DrMikeG/Lightsaber2021/readme_imgs/adafruit_products_TB6612_RasPi_stepper_bb.jpg

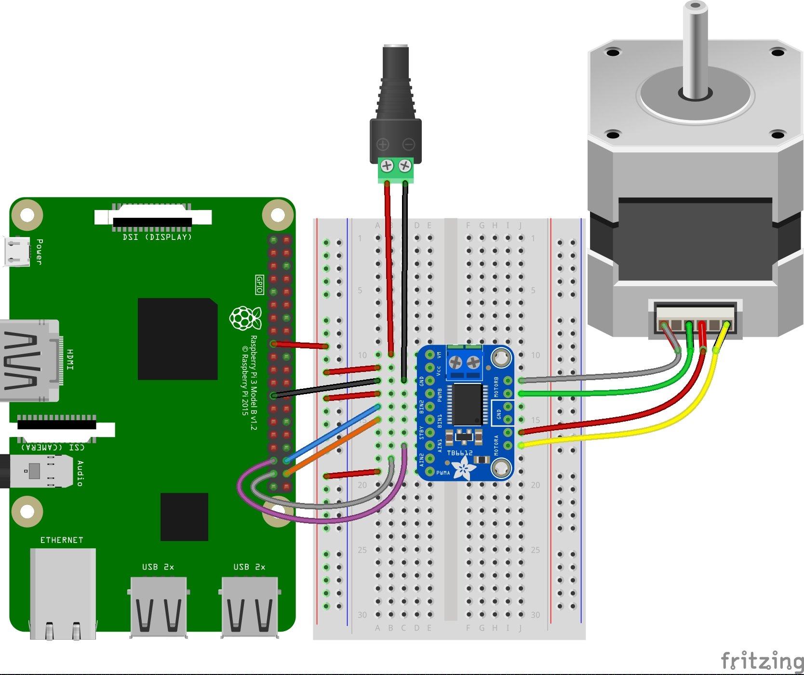
readme_imgs/adafruit_products_TB6612_RasPi_stepper_bb.jpg
