DrMikeG/Lightsaber2021/readme_imgs/circuitpython_FeatherM0ExpressPot_bb.jpg

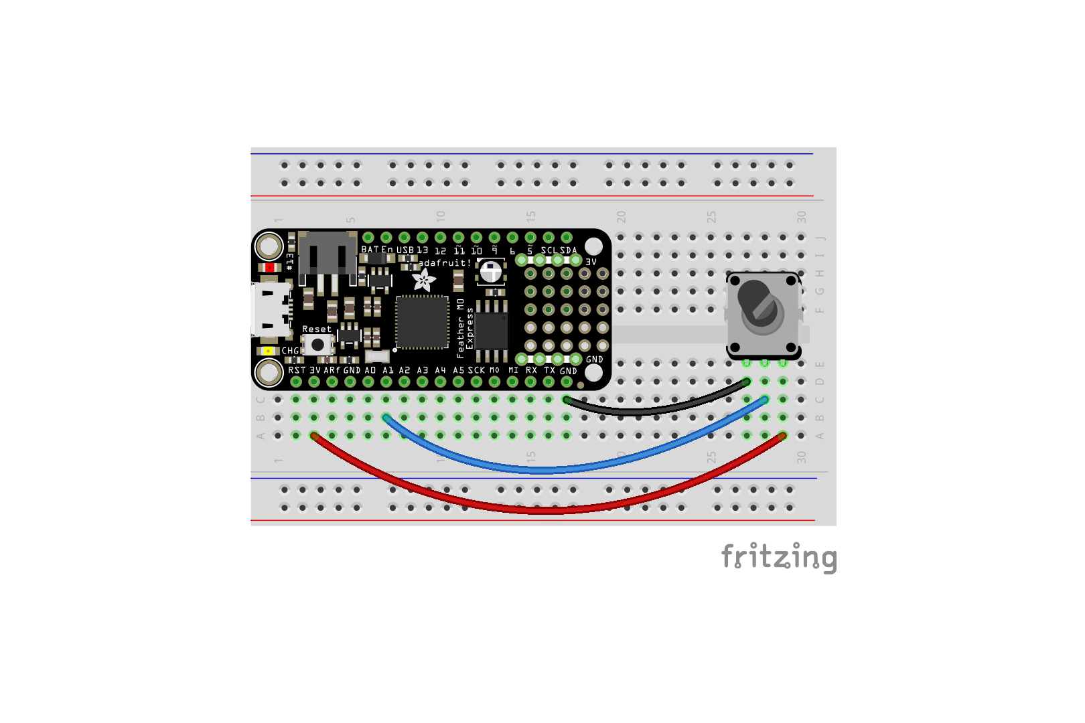
readme_imgs/circuitpython_FeatherM0ExpressPot_bb.jpg
