DrMikeG/Lightsaber2021/readme_imgs/Push-Pull-Pots.jpg

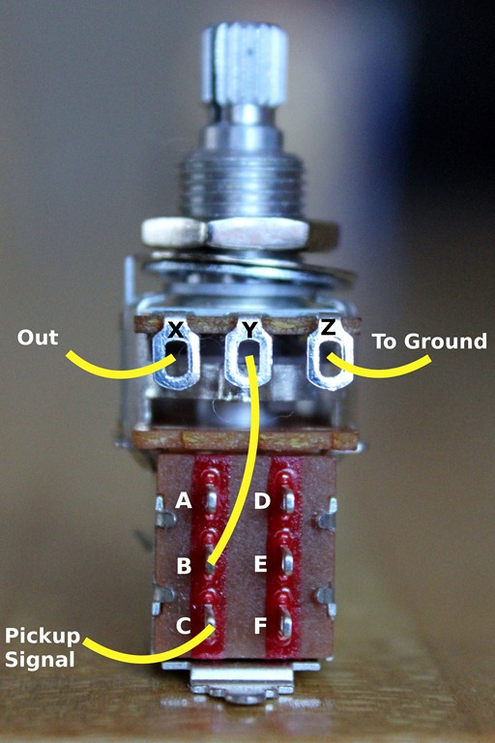
readme_imgs/Push-Pull-Pots.jpg
