DrMikeG/Lightsaber2021/readme_imgs/robotics___cnc_pico_motor_party_rev1_1.jpg

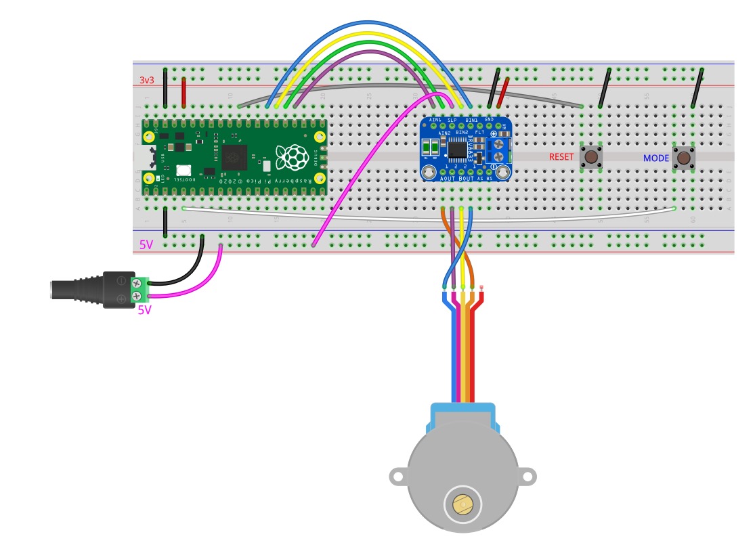
readme_imgs/robotics___cnc_pico_motor_party_rev1_1.jpg
