DrMikeG/Lightsaber2021/PropMaker_LightSaber_parts/images/1a010fce53cceae1ac56e08a0f01a03c_preview_featured.jpg

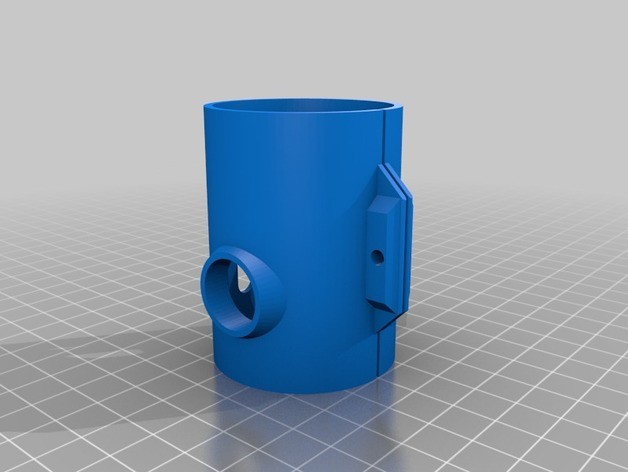
PropMaker_LightSaber_parts/images/1a010fce53cceae1ac56e08a0f01a03c_preview_featured.jpg
