DrMikeG/Lightsaber2021/PropMaker_LightSaber_parts/images/1e69a8725f925d21972f3fd7c3aa4356_preview_featured.jpg

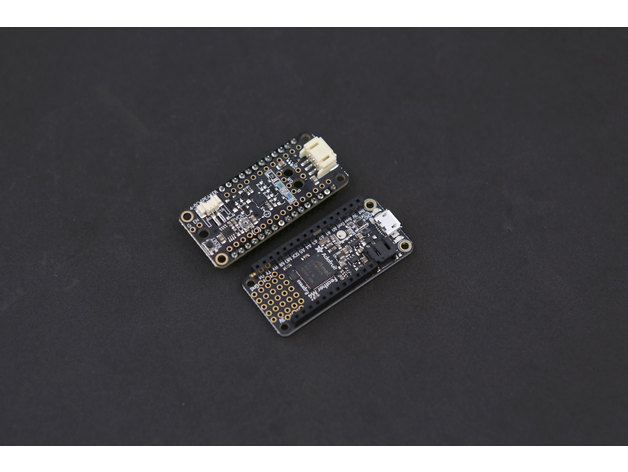
PropMaker_LightSaber_parts/images/1e69a8725f925d21972f3fd7c3aa4356_preview_featured.jpg
