DrMikeG/Lightsaber2021/PropMaker_LightSaber_parts/images/2a8135917e567a2e131dea8dfad645b4_preview_featured.jpg

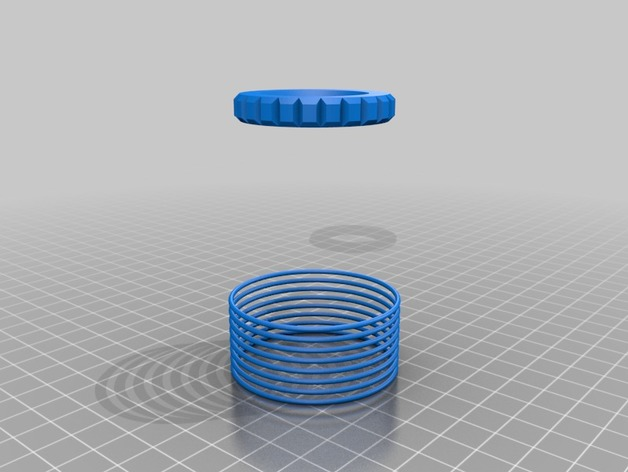
PropMaker_LightSaber_parts/images/2a8135917e567a2e131dea8dfad645b4_preview_featured.jpg
