DrMikeG/Lightsaber2021/PropMaker_LightSaber_parts/images/2da9e44c6a2c6dd28a2d1fa6bc67a7b8_preview_featured.jpg

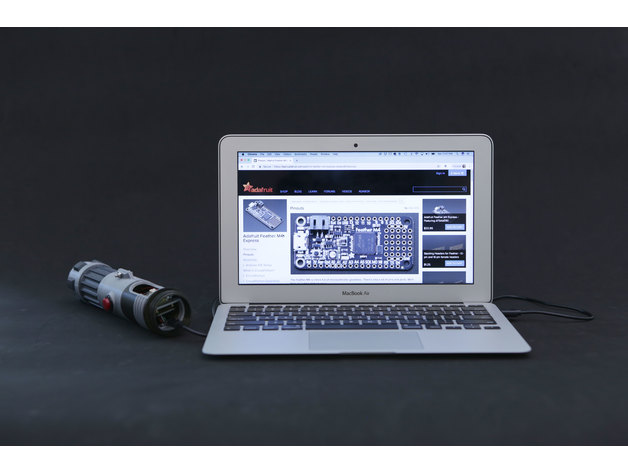
PropMaker_LightSaber_parts/images/2da9e44c6a2c6dd28a2d1fa6bc67a7b8_preview_featured.jpg
