DrMikeG/Lightsaber2021/PropMaker_LightSaber_parts/images/4b34a5e26058de7491f0624bd9dabff6_preview_featured.jpg

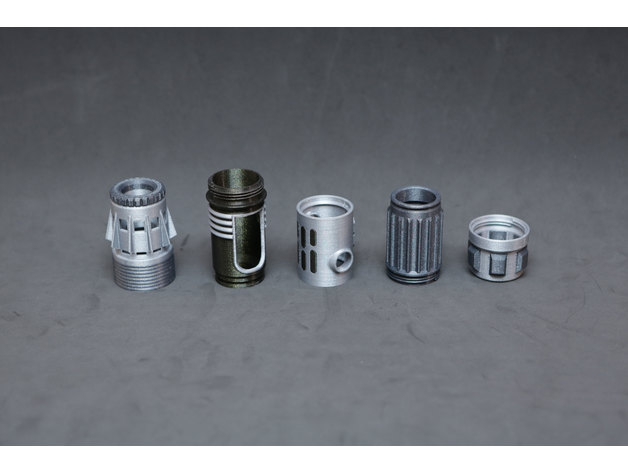
PropMaker_LightSaber_parts/images/4b34a5e26058de7491f0624bd9dabff6_preview_featured.jpg
