DrMikeG/Lightsaber2021/PropMaker_LightSaber_parts/images/5d4f0135c1b05c36856adea3e5bb96b0_preview_featured.jpg

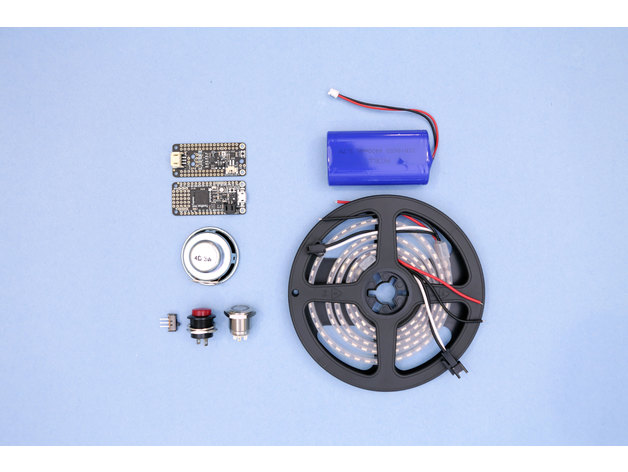
PropMaker_LightSaber_parts/images/5d4f0135c1b05c36856adea3e5bb96b0_preview_featured.jpg
