DrMikeG/Lightsaber2021/PropMaker_LightSaber_parts/images/5df59d24ba937bf4968393d7608ab2a4_preview_featured.jpg

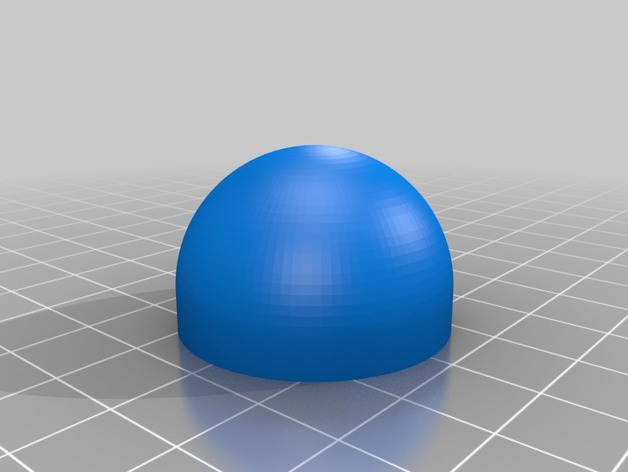
PropMaker_LightSaber_parts/images/5df59d24ba937bf4968393d7608ab2a4_preview_featured.jpg
