DrMikeG/Lightsaber2021/PropMaker_LightSaber_parts/images/6a94d57f789392ea3bade564f7ede461_preview_featured.jpg

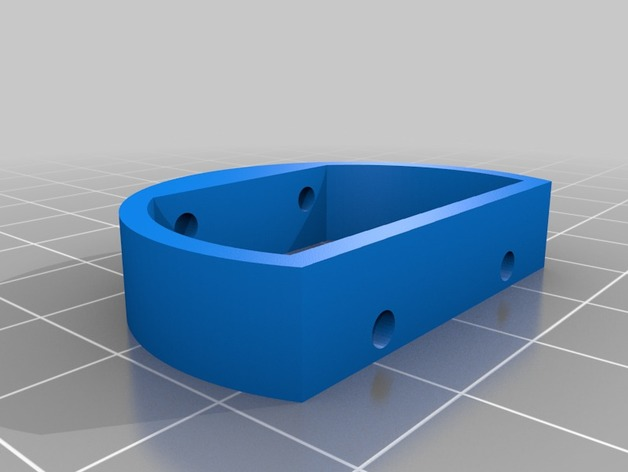
PropMaker_LightSaber_parts/images/6a94d57f789392ea3bade564f7ede461_preview_featured.jpg
