DrMikeG/Lightsaber2021/PropMaker_LightSaber_parts/images/6db03532910a7f3d1109cc5c1272abf1_preview_featured.jpg

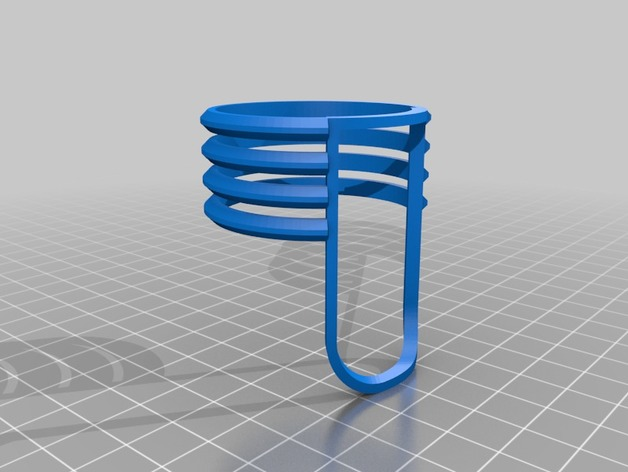
PropMaker_LightSaber_parts/images/6db03532910a7f3d1109cc5c1272abf1_preview_featured.jpg
