DrMikeG/Lightsaber2021/PropMaker_LightSaber_parts/images/37e0bd1d6943ed3912d0251d179854dd_preview_featured.jpg

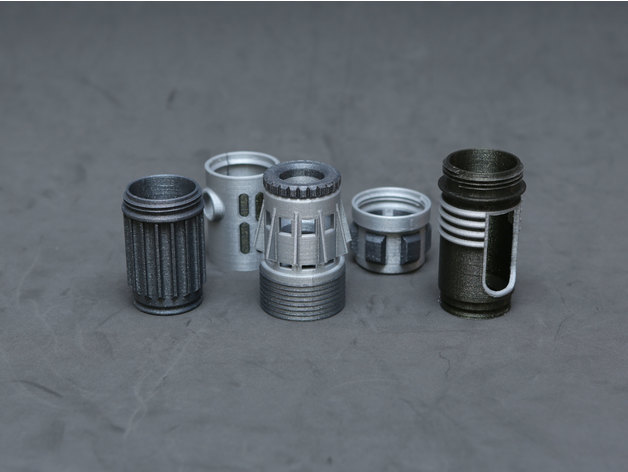
PropMaker_LightSaber_parts/images/37e0bd1d6943ed3912d0251d179854dd_preview_featured.jpg
