DrMikeG/Lightsaber2021/PropMaker_LightSaber_parts/images/97de8b0ce98b56c74fa4f8f1e708dd70_preview_featured.jpg

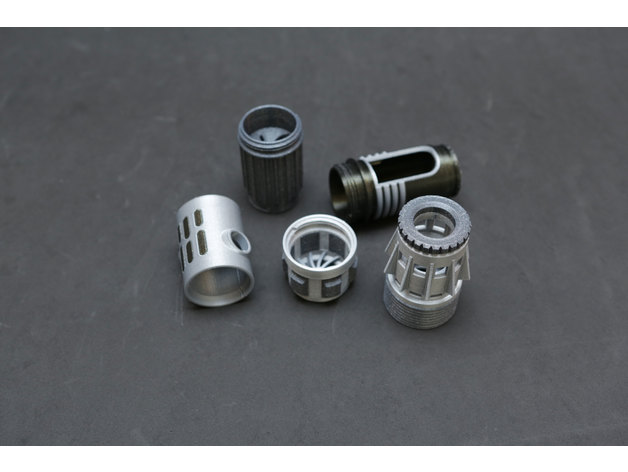
PropMaker_LightSaber_parts/images/97de8b0ce98b56c74fa4f8f1e708dd70_preview_featured.jpg
