DrMikeG/Lightsaber2021/PropMaker_LightSaber_parts/images/725ce138789fb76293f7604e14eeec18_preview_featured.jpg

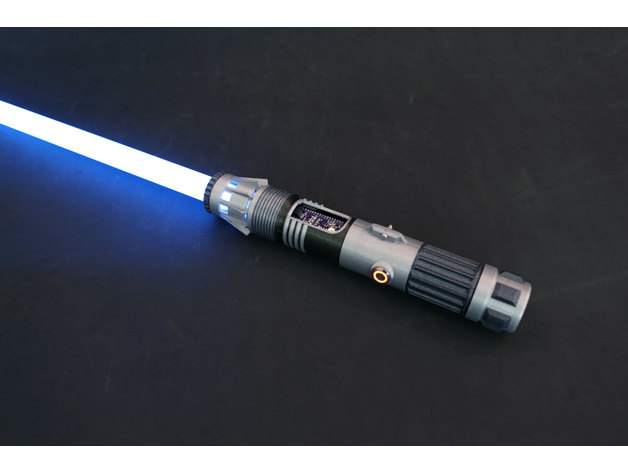
PropMaker_LightSaber_parts/images/725ce138789fb76293f7604e14eeec18_preview_featured.jpg
