DrMikeG/Lightsaber2021/PropMaker_LightSaber_parts/images/0832f2631e51cb04565bbbbad0c780f9_preview_featured.jpg

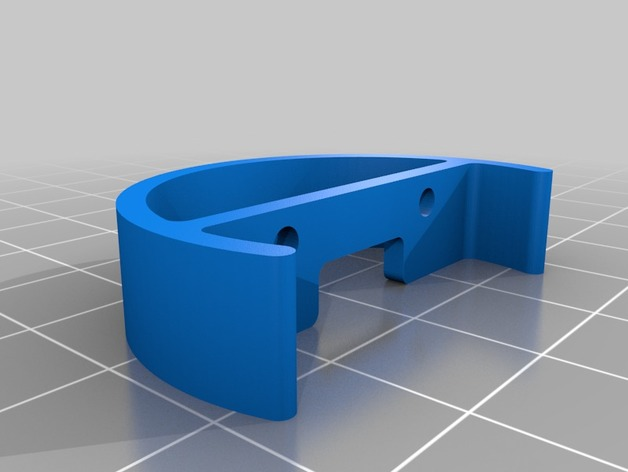
PropMaker_LightSaber_parts/images/0832f2631e51cb04565bbbbad0c780f9_preview_featured.jpg
