DrMikeG/Lightsaber2021/PropMaker_LightSaber_parts/images/8650a7c8c6fc7279c6bf91dc1d254c43_preview_featured.jpg

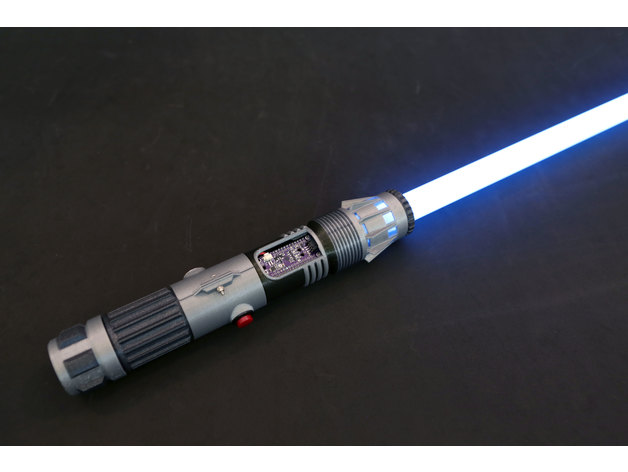
PropMaker_LightSaber_parts/images/8650a7c8c6fc7279c6bf91dc1d254c43_preview_featured.jpg
