DrMikeG/Lightsaber2021/PropMaker_LightSaber_parts/images/abff16dfec9813ce94c728e3b09540b0_preview_featured.jpg

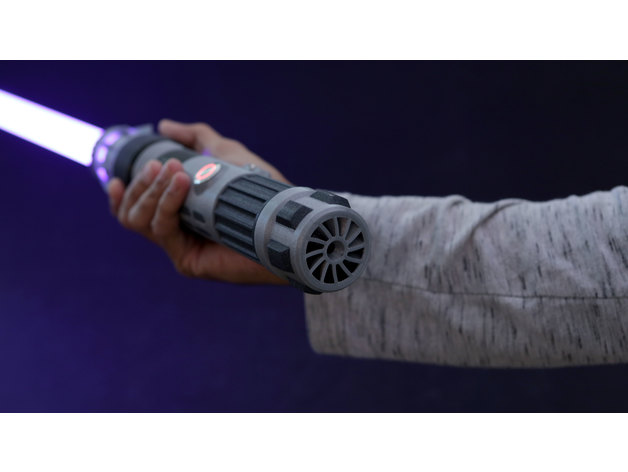
PropMaker_LightSaber_parts/images/abff16dfec9813ce94c728e3b09540b0_preview_featured.jpg
