DrMikeG/Lightsaber2021/PropMaker_LightSaber_parts/images/ad7b09b95d9fd7f6477543790e99b3de_preview_featured.jpg

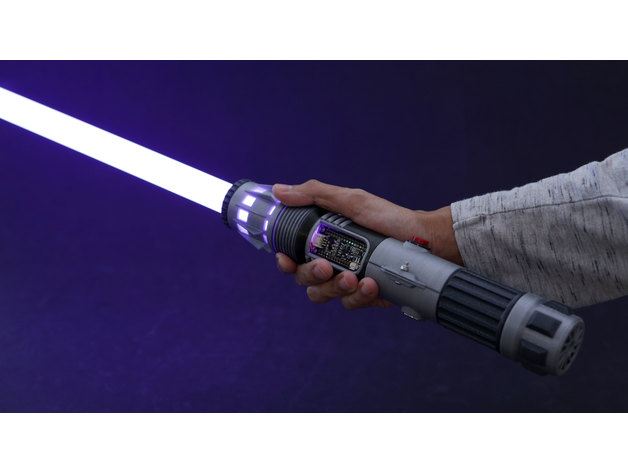
PropMaker_LightSaber_parts/images/ad7b09b95d9fd7f6477543790e99b3de_preview_featured.jpg
