DrMikeG/Lightsaber2021/PropMaker_LightSaber_parts/images/b92e24ca351e6c013bbf433e4f9a59d8_preview_featured.jpg

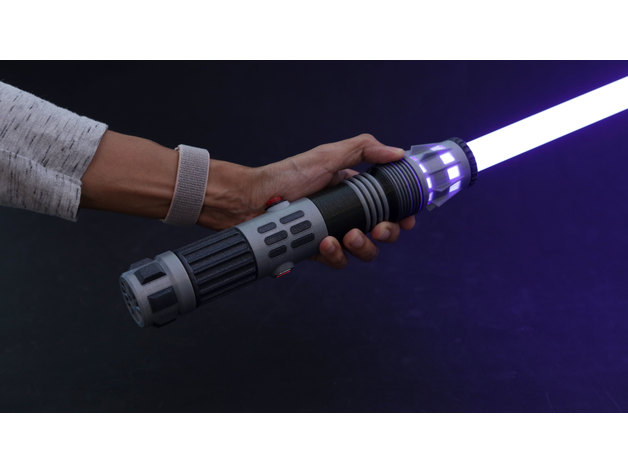
PropMaker_LightSaber_parts/images/b92e24ca351e6c013bbf433e4f9a59d8_preview_featured.jpg
