DrMikeG/Lightsaber2021/PropMaker_LightSaber_parts/images/bd8d993e79c6061508dadcb1885ae99c_preview_featured.jpg

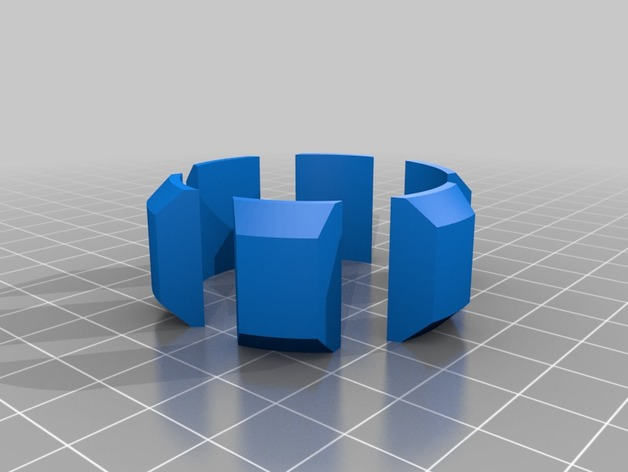
PropMaker_LightSaber_parts/images/bd8d993e79c6061508dadcb1885ae99c_preview_featured.jpg
