DrMikeG/Lightsaber2021/PropMaker_LightSaber_parts/images/d68c645e9b058e6467c144a842382a89_preview_featured.jpg

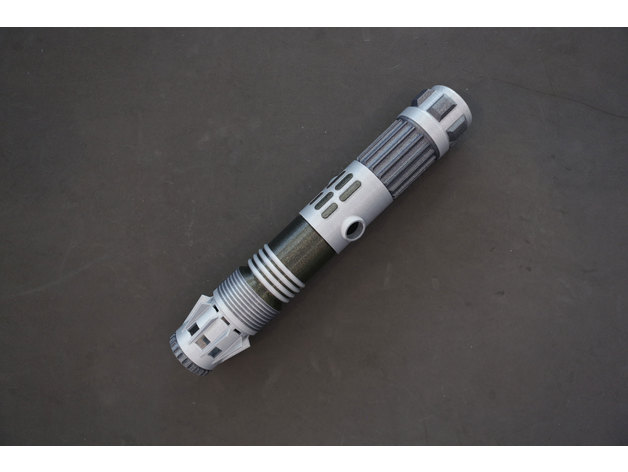
PropMaker_LightSaber_parts/images/d68c645e9b058e6467c144a842382a89_preview_featured.jpg
