DrMikeG/Lightsaber2021/PropMaker_LightSaber_parts/images/e01a0911875ea568462dee74d059c374_preview_featured.jpg

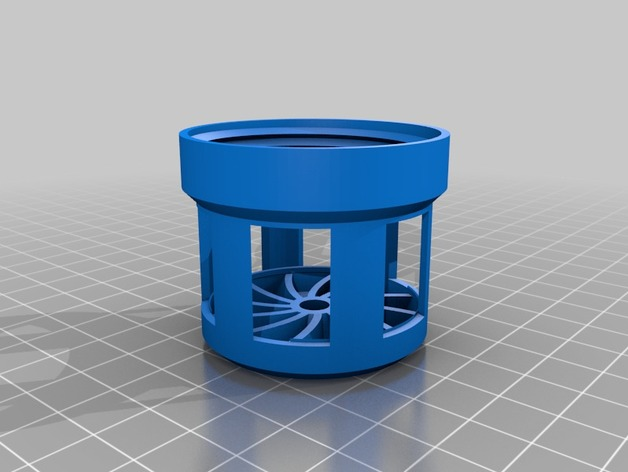
PropMaker_LightSaber_parts/images/e01a0911875ea568462dee74d059c374_preview_featured.jpg
