DrMikeG/Lightsaber2021/PropMaker_LightSaber_parts/images/e013908a4d9d27399bb73e748257cb8e_preview_featured.jpg

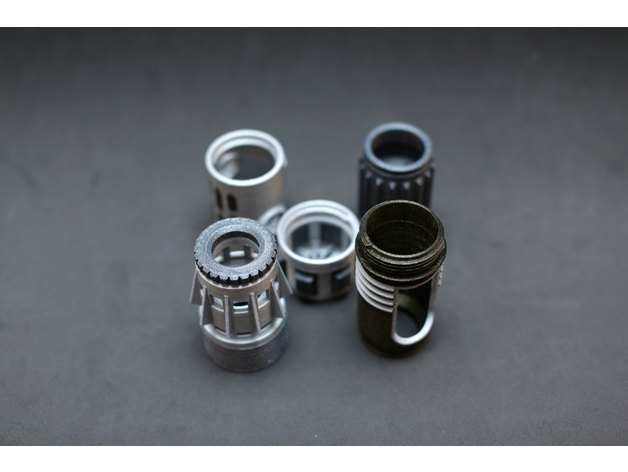
PropMaker_LightSaber_parts/images/e013908a4d9d27399bb73e748257cb8e_preview_featured.jpg
