DrMikeG/Lightsaber2021/PropMaker_LightSaber_parts/images/f410defe41d23869d9bcb78284f8b42a_preview_featured.jpg

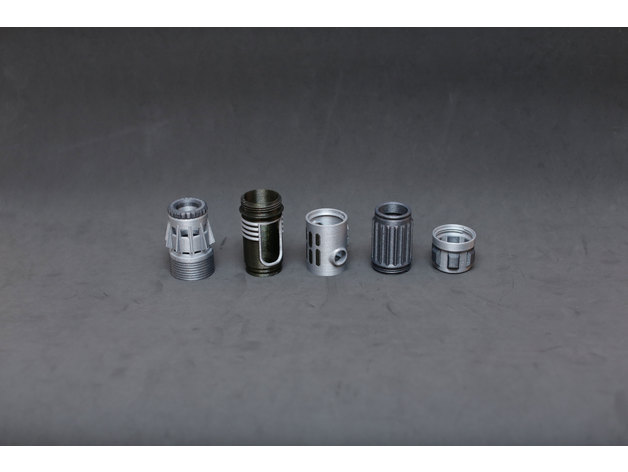
PropMaker_LightSaber_parts/images/f410defe41d23869d9bcb78284f8b42a_preview_featured.jpg
