DrMikeG/Lightsaber2021/PropMaker_LightSaber_parts/images/f34448d2e517d34961dc217db62863bf_preview_featured.jpg

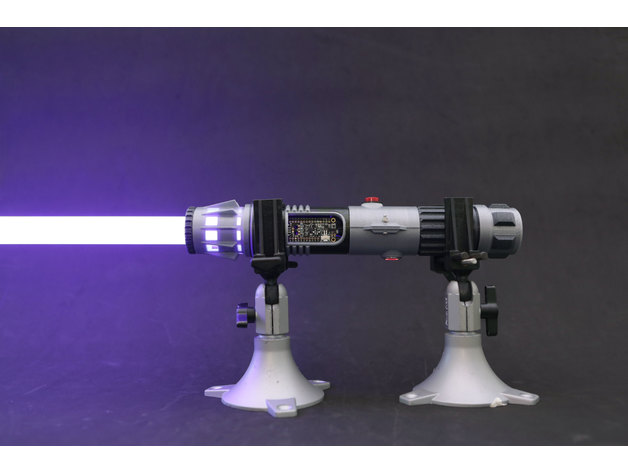
PropMaker_LightSaber_parts/images/f34448d2e517d34961dc217db62863bf_preview_featured.jpg
