DrMikeG/Lightsaber2021/PropMaker_LightSaber_parts/files/fwls-clamp-single.stl

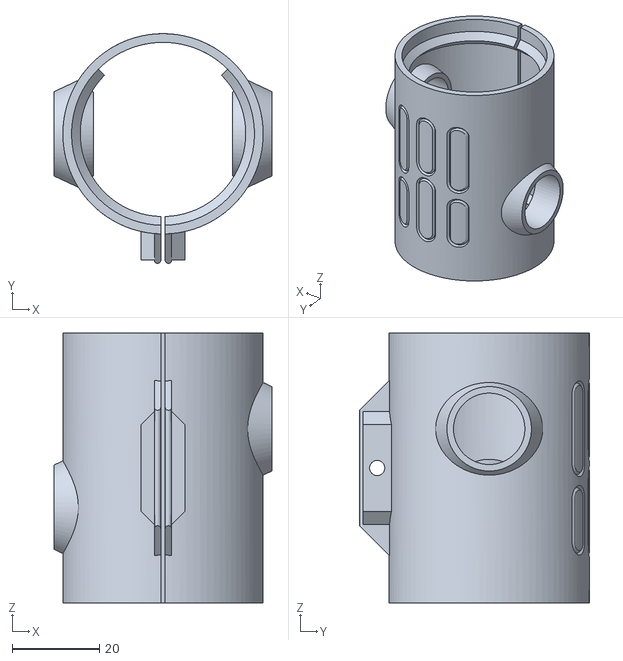
[picture p47: CAD file, 2021-08-30]
PropMaker_LightSaber_parts/files/fwls-clamp-single.stl
50.0 x 52.8 x 62.0
