DrMikeG/Lightsaber2021/PropMaker_LightSaber_parts/files/multimats/fwls-pommel-b.stl

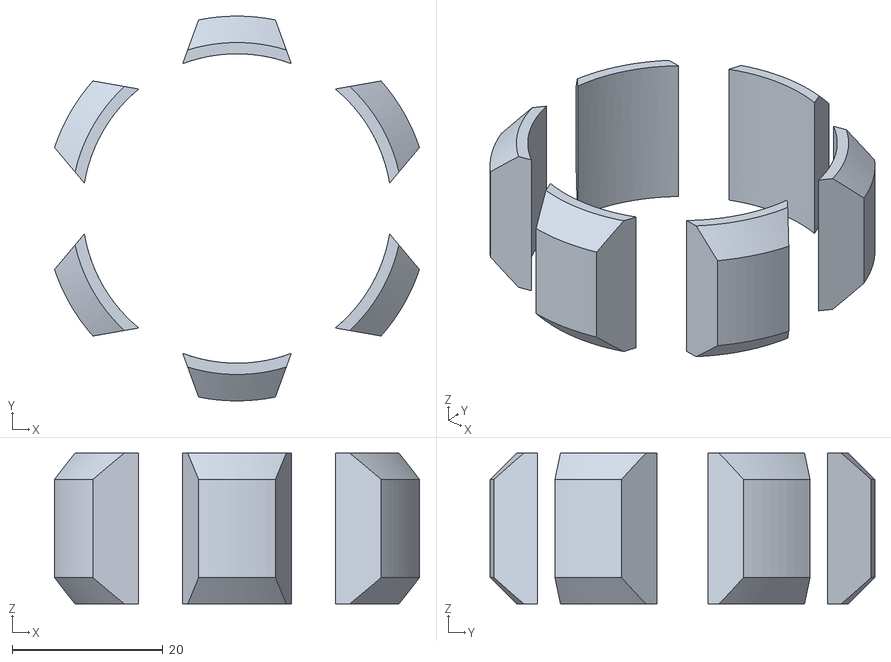
[picture p48: CAD file, 2021-08-30]
PropMaker_LightSaber_parts/files/multimats/fwls-pommel-b.stl
48.4 x 51.0 x 20.0
