DrMikeG/Lightsaber2021/parts/BatteryHousing03.stl

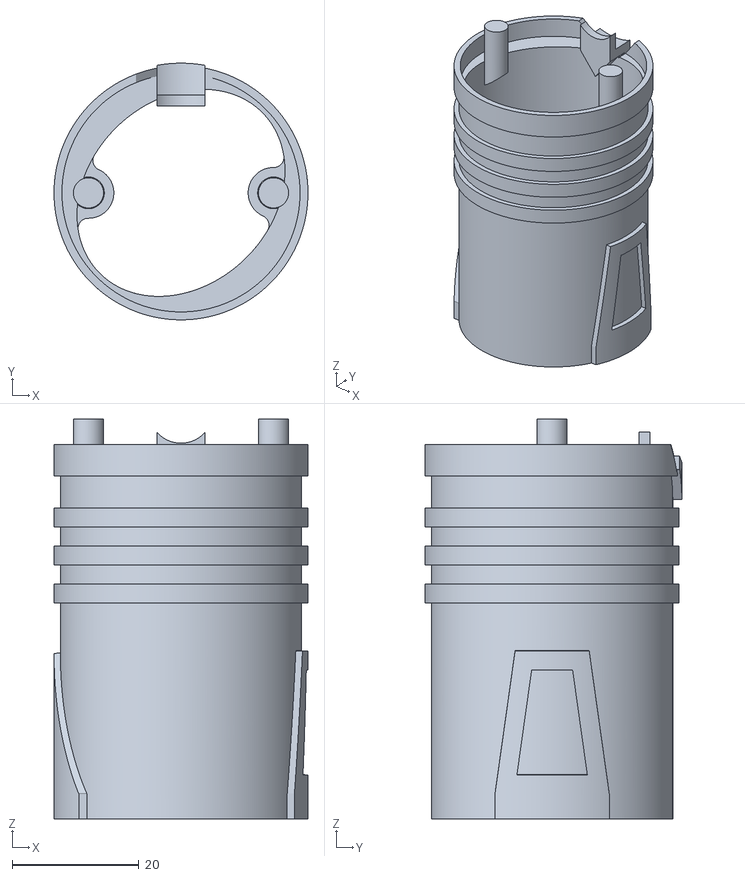
[picture p49: CAD file, 2021-09-21]
parts/BatteryHousing03.stl
40.0 x 40.4 x 63.0
