DrMikeG/Lightsaber2021/PropMaker_LightSaber_parts/files/fwls-wing-mount.stl

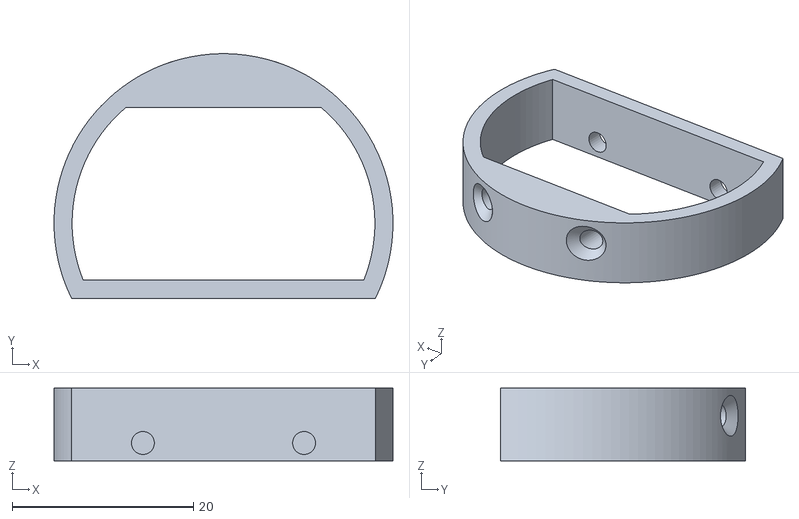
[picture p50: CAD file, 2021-08-30]
PropMaker_LightSaber_parts/files/fwls-wing-mount.stl
37.4 x 27.0 x 8.00
