DrMikeG/Lightsaber2021/PropMaker_LightSaber_parts/files/multimats/fwls-barrel-b.stl

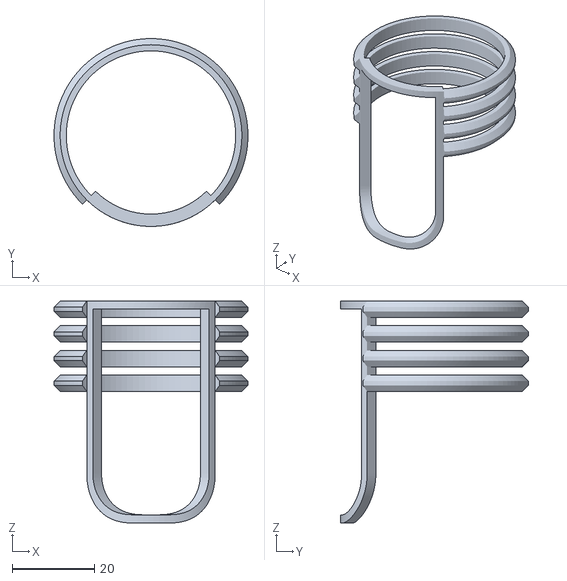
[picture p51: CAD file, 2021-08-30]
PropMaker_LightSaber_parts/files/multimats/fwls-barrel-b.stl
47.2 x 45.7 x 54.0
