DrMikeG/Lightsaber2021/parts/LedSupport01.stl

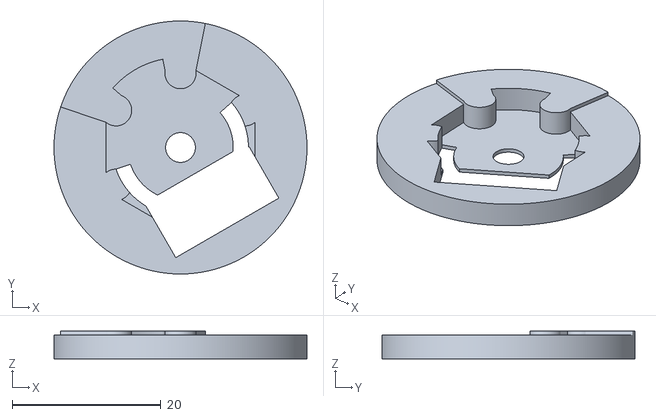
[picture p52: CAD file, 2021-09-21]
parts/LedSupport01.stl
34.0 x 34.0 x 3.70
