DrMikeG/Lightsaber2021/PropMaker_LightSaber_parts/files/fwls-powercell.stl

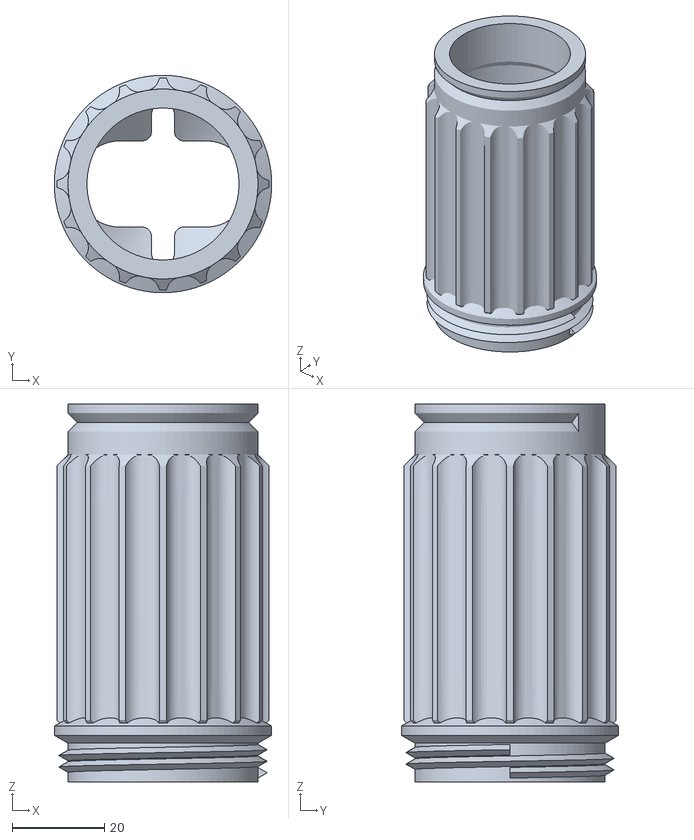
[picture p53: CAD file, 2021-08-30]
PropMaker_LightSaber_parts/files/fwls-powercell.stl
47.2 x 47.2 x 82.0
