DrMikeG/Lightsaber2021/PropMaker_LightSaber_parts/files/multimats/fwls-clamp-b.stl

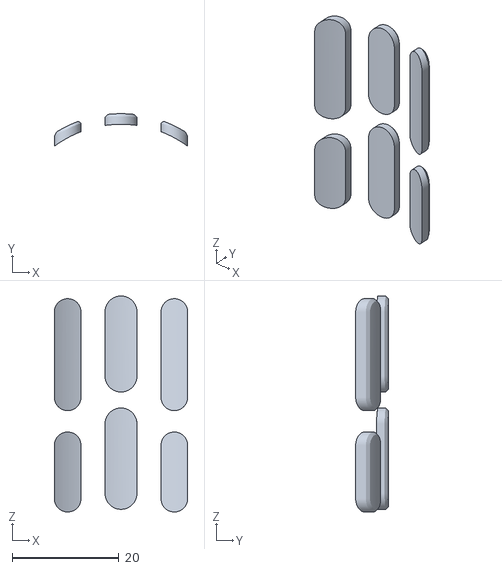
[picture p54: CAD file, 2021-08-30]
PropMaker_LightSaber_parts/files/multimats/fwls-clamp-b.stl
25.0 x 6.13 x 40.5
