DrMikeG/Lightsaber2021/parts/SwitchHousing03.stl

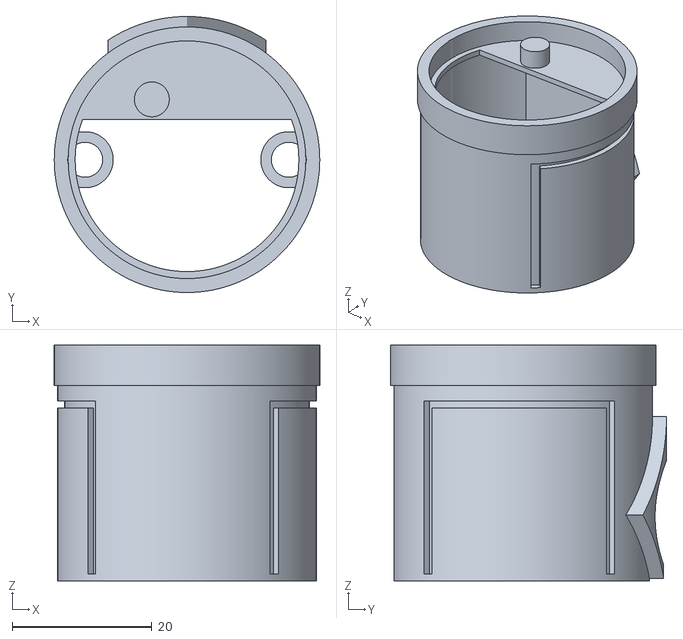
[picture p55: CAD file, 2021-09-21]
parts/SwitchHousing03.stl
38.0 x 39.5 x 33.7
