DrMikeG/Lightsaber2021/parts/SwitchHousing02.stl

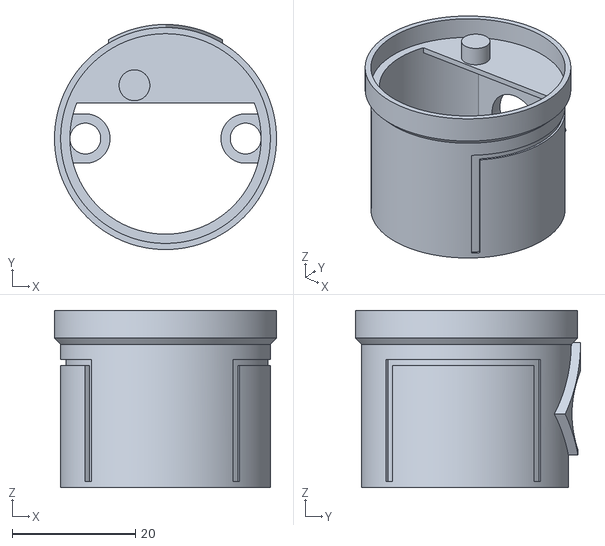
[picture p56: CAD file, 2021-09-21]
parts/SwitchHousing02.stl
36.0 x 36.5 x 28.7
