DrMikeG/Lightsaber2021/parts/SpeakerHousinga_01.stl

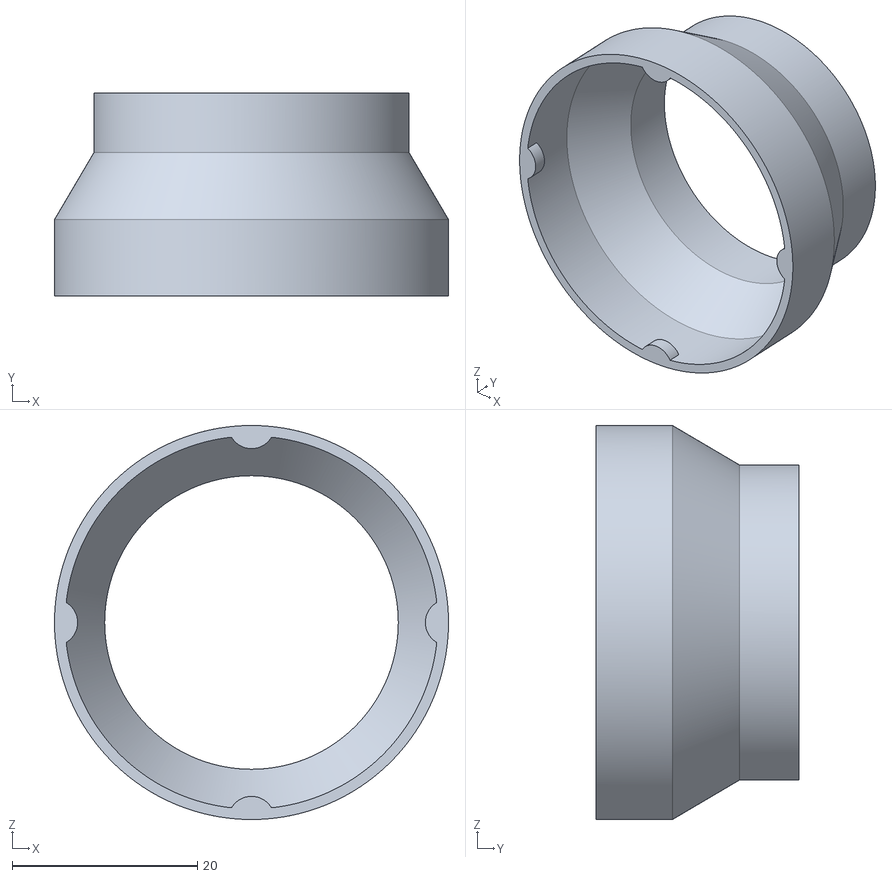
[picture p57: CAD file, 2021-08-30]
parts/SpeakerHousinga_01.stl
42.5 x 21.9 x 42.5
