DrMikeG/Lightsaber2021/parts/Helix02.stl

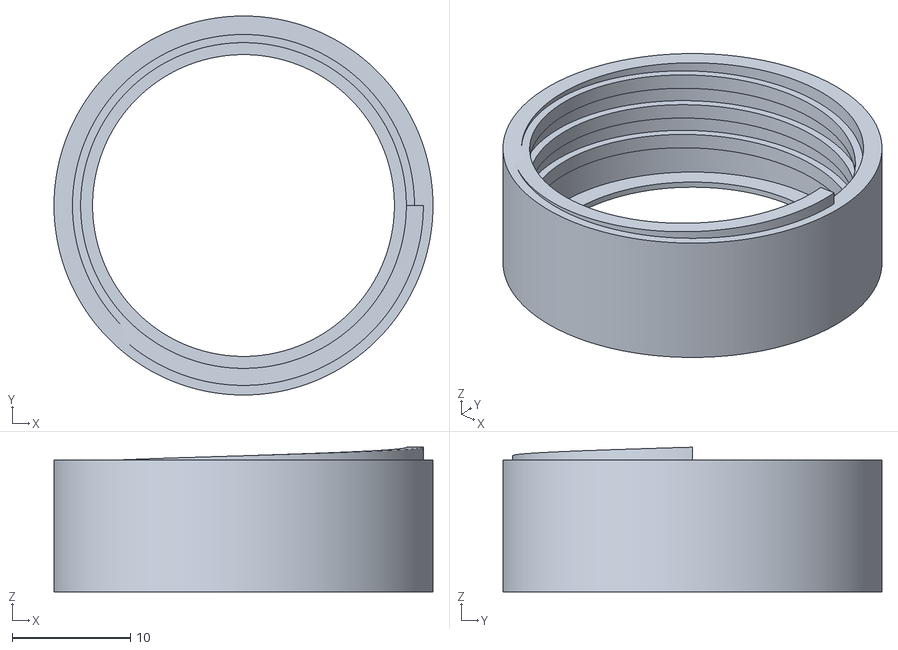
[picture p58: CAD file, 2021-08-30]
parts/Helix02.stl
32.0 x 32.0 x 12.2
