DrMikeG/Lightsaber2021/parts/SpeakerHousing_01.stl

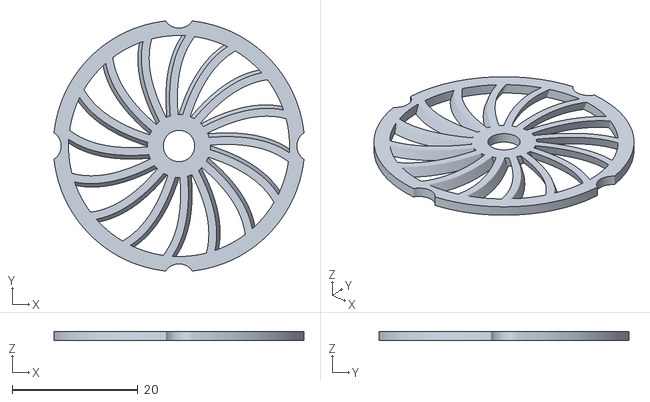
[picture p59: CAD file, 2021-08-30]
parts/SpeakerHousing_01.stl
39.8 x 39.8 x 1.50
