DrMikeG/Lightsaber2021/parts/LipoShell1.stl

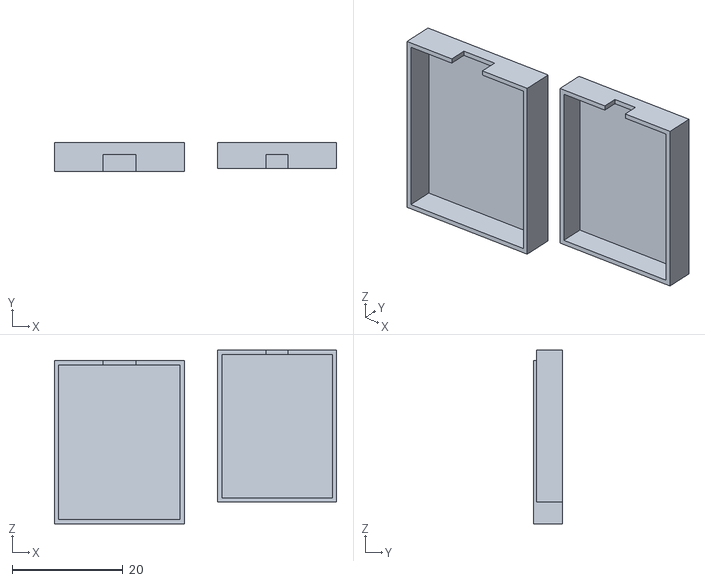
[picture p60: CAD file, 2021-08-30]
parts/LipoShell1.stl
51.0 x 5.25 x 31.4
