DrMikeG/Lightsaber2021/parts/Helix03.stl

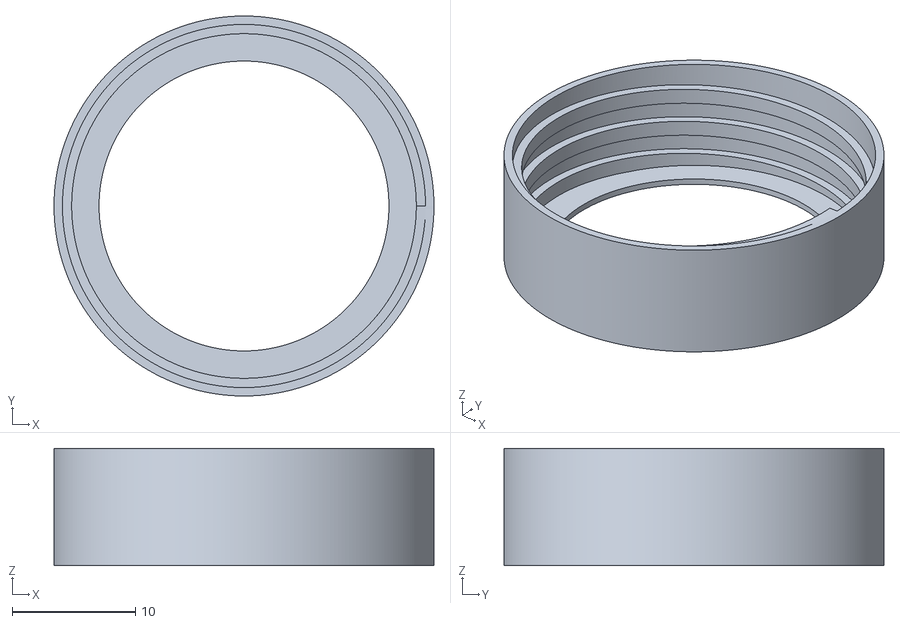
[picture p61: CAD file, 2021-08-30]
parts/Helix03.stl
30.9 x 30.9 x 9.55
