DrMikeG/Lightsaber2021/3d_printing_light-wand-circuit-diagram.jpg

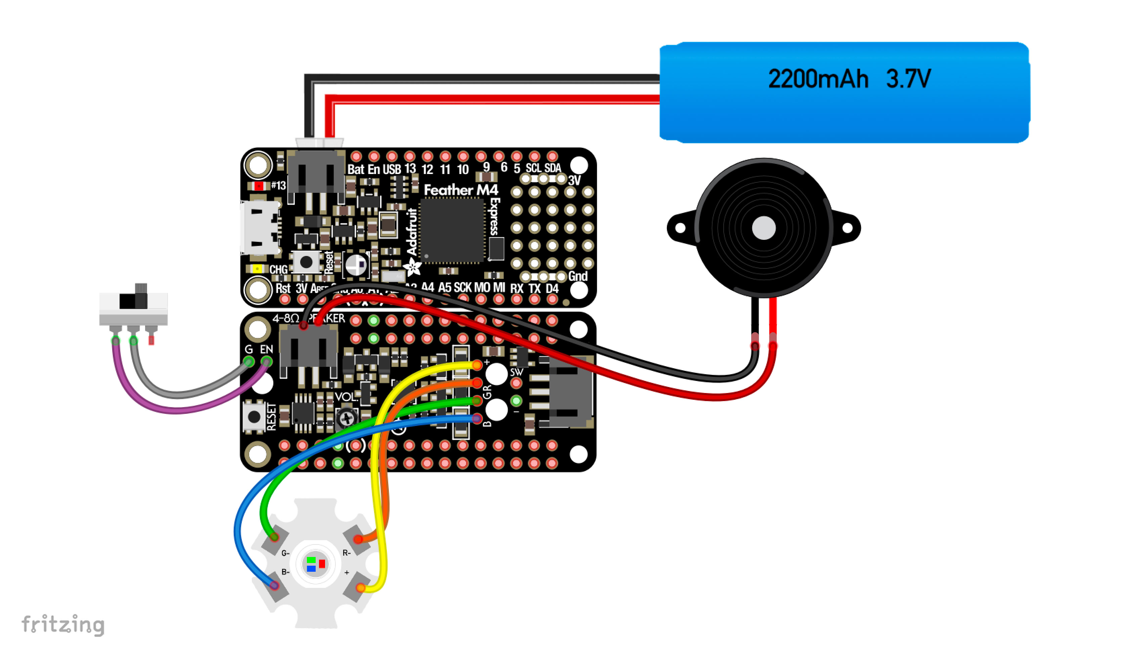
3d_printing_light-wand-circuit-diagram.jpg
